Krupamc/keypad_2026/firmware/kmk_firmware-main/boards/Pico14/README.md

# Pico 14 Numerical Keypad

Pico14

Pico 14 Numerical Keypad / Macro Pad PCBs and Hardware Kit.

`kb.py` is designed to work with the Pi Pico.
